nodep/myAmp/sym/inrush.asc

C1: cap; 330n
C2: cap; 1000µ
C3: cap; 330n
C4: cap; 1000µ
M1: nmos; irfs52n15d
M2: pmos; irf4905
R1: res; 470k
R2: res; 470k
R3: res; 1Meg
R4: res; 1Meg
Rload_m: res; 100
Rload_p: res; 100
Rtest_n: res; 1µ
Rtest_r: res; 1µ
V1: voltage; 25
V2: voltage; 25
Named nets: 0, gn, gp, sp
.tran 1 startup
.inc irfs52n15d.txt
.inc irf4905.txt
