nodep/myAmp/sym/mixer.asc

C1: cap; 1µ
C2: cap; 1µ
C3: cap; 10µ
R1: res; 10k
R3: res; 10k
R4: res; 10k
R5: res; 10k
R6: res; {dry*10k + 1m}
R7: res; {(1 - dry)*10k + 1m}
R8: res; 470k
R9: res; {vol*22k + 1m}
U1: opamp2; tl072
V1: voltage; SINE(0 1 1k)
V2: voltage; SINE(0 1 2k3)
V3: voltage; 5
V4: voltage; 2.5
Named nets: 0, VCC, VREF, dry, wet, out
.option numdgt = 7
.option plotwinsize = 0
.inc TL072.sub
.param dry 1
.param vol 1
.tran 0 10m 0 1u
