nodep/myAmp/sym/preamp-esp27.asc

C1: cap; 100n
C2: cap; 22n
C3: cap; 1µ
C4: cap; 120p
C5: cap; 250p
C6: cap; 100n
C7: cap; 47n
C8: cap; 1µ
C10: cap; 120p
C11: cap; 2µ2
D1: diode; 1N4148
D2: diode; 1N4148
D3: diode; 1N4148
D4: diode; 1N4148
P1a: res; {(1 - ptt)*250k + 1m}
P1b: res; {ptt*250k + 1m}
P2: res; {ptb*250k + 1m}
P3: res; {ptm*10k + 1m}
P5a: res; {(1 - ptv)*50k + 1m}
P5b: res; {ptv*50k + 1m}
R1: res; 100k
R3: res; 1Meg
R4: res; 1k
R5: res; 1k
R6: res; 10k
R7: res; 10k
R8: res; 100k
R9: res; 1k
R10: res; 1Meg
R11: res; 10k
R12: res; 10k
R13: res; 4k7
R14: res; 220
R15: res; 2k2
R16: res; 100k
R17: res; 220
R18: res; 10k
R19: res; 1Meg
U1: opamp2; TL072
U2: opamp2; TL072
U3: opamp2; TL072
U4: opamp2; TL072
V1: voltage; SINE(0 0.8 3k); AC 1
V2: voltage; 24
V3: voltage; 12
Named nets: VGND, 0, Vpow, out, in, stage1, stage2, stage3, clipped
.inc OPAx134.lib
.inc NE5532.txt
.inc TL072.sub
.tran 20m
.param ptt 1
.param ptm 1
.param ptb 1
.param ptv 1
