nodep/myAmp/src/app.cpp

#include <stdio.h>
#include <stdlib.h>

#include <avr/io.h>
#include <avr/pgmspace.h>
#include <util/delay.h>

#include "hw.h"
#include "avrdbg.h"
#include "app.h"
#include "adc.h"
#include "powamp.h"
#include "programs.h"
#include "graphtext.h"

App::App()
{
	display.init();
	fill(display, colBlack);
	display.backlight_on();

	//ts.init();

	// init the ADC sources
	adc.set_muxpos(0, ADC_MUXPOS_AIN7_gc, 0);
	adc.set_muxpos(1, ADC_MUXPOS_AIN10_gc, 32);
	adc.set_muxpos(2, ADC_MUXPOS_AIN11_gc, 32);
	adc.set_muxpos(3, ADC_MUXPOS_AIN12_gc, 32);
	adc.set_muxpos(4, ADC_MUXPOS_AIN13_gc, 32);

	Preset::dump_eeprom_presets();

	////testing fonts
	//hline(display, 0, 0, 320, colRed);
	//set_large_font(FreeSans9pt7b);			print_large(display, "P",  5, 0, colYellow);
	//set_large_font(FreeSans12pt7b);			print_large(display, "P", 20, 0, colYellow);
	//set_large_font(FreeSans18pt7b);			print_large(display, "P", 37, 0, colYellow);
	//set_large_font(FreeSans24pt7b);			print_large(display, "P", 55, 0, colYellow);
	//set_large_font(FreeSansBold9pt7b);		print_large(display, "P", 80, 0, colYellow);
	//set_large_font(FreeSansBold12pt7b);		print_large(display, "P", 95, 0, colYellow);
	//set_large_font(FreeSansBold18pt7b);		print_large(display, "P", 115, 0, colYellow);
	//set_large_font(FreeSansBold24pt7b);		print_large(display, "P", 135, 0, colYellow);
	//while (1);

	// wait until the ADC stabilizes
	for (int8_t i = 0; i < 10; i++)
	{
		while (!adc.has_fresh_set())
			;
	}

	// draw the pedals
	draw_exp_pedal(90, 185, colWhite);
	draw_ftsw_pedal(190, 180, colWhite);

	// load the active preset
	Preset preset;
	preset.load_active_prog();
	fv1.set_preset(preset);
	refresh_preset();

	pedals.reset();
}

void App::poll()
{
	powamp_poll();

	Preset current_preset = fv1.get_active_preset();

	// check and handle the ADC
	if (adc.has_fresh_set())
	{
		// convert ADC result to voltage
		refresh_voltage(adc.results[0] / ADC_VOLTAGE_FACTOR);

		if (adc.has_changed[1])
			current_preset.pots[0] = 0x1000 - (adc.results[1] >> 4);

		if (adc.has_changed[2])
			current_preset.pots[1] = 0x1000 - (adc.results[2] >> 4);

		if (adc.has_changed[3])
			current_preset.pots[2] = 0x1000 - (adc.results[3] >> 4);

		if (adc.has_changed[4]  &&  !exp_pedal_active)
			current_preset.mix = 0xff - (adc.results[4] >> 8);
	}

	bool preset_saved = false;
	const auto button_event = rotenc.get_button_event();
	if (button_event == RotEnc::beDouble)
		preset_saved = current_preset.save();
	else if (button_event != RotEnc::beNone)
		dprint("button event: %s\n", RotEnc::get_button_event_desc(button_event));

	const auto delta = rotenc.get_delta();
	if (delta)
	{
		int16_t new_prog_num = current_preset.prog_num + delta;
		if (new_prog_num < 0)
			new_prog_num = NUM_FV1_PROGRAMS - 1;
		if (new_prog_num >= NUM_FV1_PROGRAMS)
			new_prog_num = 0;

		// load the preset if it changed
		if (current_preset.prog_num != new_prog_num)
		{
			current_preset.load(new_prog_num);
			current_preset.save_active_prog();
		}
	}

	// handle pedal events
	for (;;)
	{
		const PedalEvent event = pedals.get_event();

		if (event == evNone)
			break;
			
		if (event == evExpPosition)
		{
			dprint("evExpPos\n");

			if (exp_pedal_active)
			{
				const uint16_t exp_range = pedals.get_position_range();
				if (exp_range)
				{
					const double dest_range = 0x100;
					const double factor = exp_range / dest_range;
					const uint16_t calib_pos = static_cast<uint16_t>(pedals.exp_position / factor);
					current_preset.mix = calib_pos > 0xff ? 0xff : calib_pos;
				}
			}
		}
		else if (event == evExpInit)
		{
			dprint("evExpInit\n");

			pedals.set_led(ledExpGreen);
			pedals.clear_led(ledExpRed);

			// exp pedal is present but not active
			exp_pedal_active = false;
		}
		else if (event == evExpBtnDown)
		{
			dprint("evExpBtnDown\n");

			exp_pedal_active = !exp_pedal_active;
			if (exp_pedal_active)
				pedals.set_led(ledExpRed);
			else
				pedals.clear_led(ledExpRed);
		}
		else if (event == evFtswInit)
		{
			dprint("evFtswInit\n");
			pedals.set_ftsw_number(current_preset.prog_num);
		}
		else if (event == evFtswBtn1Down)
		{
			uint8_t new_prog_num = current_preset.prog_num + 1;
			if (new_prog_num >= NUM_FV1_PROGRAMS)
				new_prog_num = 0;

			current_preset.load(new_prog_num);
			current_preset.save_active_prog();

			pedals.set_led(ledFtswModeTuner);
		}
		else if (event == evFtswBtn1Up)
		{
			pedals.clear_led(ledFtswModeTuner);
		}
		else if (event == evFtswBtn2Down)
		{
			pedals.set_led(ledFtswQA1);
		}
		else if (event == evFtswBtn2Up)
		{
			pedals.clear_led(ledFtswQA1);
		}
		else if (event == evFtswBtn3Down)
		{
			pedals.set_led(ledFtswQA2);
		}
		else if (event == evFtswBtn3Up)
		{
			pedals.clear_led(ledFtswQA2);
		}
		else if (event == evFtswBtn4Down)
		{
			pedals.set_led(ledFtswQA3);
		}
		else if (event == evFtswBtn4Up)
		{
			pedals.clear_led(ledFtswQA3);
		}
	}

	if (fv1.set_preset(current_preset)  ||  preset_saved)
	{
		//dprint("prog=%u P0=%u P1=%u P2=%u mix=%u\n",
		//		current_preset.prog_num,
		//		current_preset.pots[0],
		//		current_preset.pots[1],
		//		current_preset.pots[2],
		//		current_preset.mix);

		refresh_preset();

		// change the number on the footswitch
		if (pedals.ftsw_present)
			pedals.set_ftsw_number(current_preset.prog_num);
	}
}

void App::refresh_voltage(const double battery_voltage)
{
	static uint16_t prev_refresh = 0;
	if (Watch::has_ms_passed_since(2000, prev_refresh))
	{
		// calc the length of the voltage bar
		static uint16_t prev_charge = 0;
		uint16_t curr_charge = 0;
		if (battery_voltage > MIN_VOLTAGE)
		{
			constexpr double factor = Display::Height / (MAX_VOLTAGE - MIN_VOLTAGE);
			curr_charge = static_cast<uint16_t>((battery_voltage - MIN_VOLTAGE) * factor);
			if (curr_charge > Display::Height)
				curr_charge = Display::Height;
		}

		// draw the bar if it changed
		Coord y = 0;
		Coord height = 0;
		if (curr_charge < prev_charge)
			y = Display::Height - prev_charge, height = prev_charge - curr_charge;
		else if (curr_charge > prev_charge)
			y = Display::Height - curr_charge, height = curr_charge - prev_charge;

		if (height != 0)
			fill_rect(display, 0, y, VOLTAGE_BAR_WIDTH, height, colGreen);

		// print the voltage
		static char prev_buff[6] = {0};
		char buff[6];
		sprintf(buff, "%.1fV", battery_voltage);
		if (strcmp(buff, prev_buff) != 0)
		{
			Window<48, 16> win(colBlack);
			set_large_font(FreeSans9pt7b);
			print_large(win, buff, 0, 0, colGreen);
			display.blit(win, VOLTAGE_BAR_WIDTH + 2, Display::Height - win.Height);
			strcpy(prev_buff, buff);
		}

		prev_charge = curr_charge;
		prev_refresh = Watch::now();
	}
}

void App::refresh_preset()
{
	//const auto start = Watch::now();
	static uint8_t prev_prog = 0xff;

	const Preset& preset = fv1.get_active_preset();

	// names
	char name[LONGEST_NAME];
	if (prev_prog != preset.prog_num)
	{
		// center the program name
		{
			Window<WIN_WIDTH, NAME_HEIGHT> win(colBlack);
			set_large_font(FreeSans12pt7b);
			fv1_programs[preset.prog_num].copy_name(name);

			const Coord width = get_text_width_large(name);
			const Coord x_offset = width < win.Width ? (win.Width - width) / 2 : 0;
			print_large(win, name, x_offset, 0, colWhite);
			display.blit(win, VOLTAGE_BAR_WIDTH + WIN_OFFSET, 10);
		}
			
		// print the program number
		{
			char num[4];
			sprintf(num, "%u", preset.prog_num);
			Window<44, 20> win(colBlack);
			set_large_font(FreeSans12pt7b);
			print_large(win, num, 0, 0, colWhite);
			display.blit(win, VOLTAGE_BAR_WIDTH + WIN_OFFSET, 180);
		}

		// param names
		Window<HBAR_WIDTH, PARAM_NAME_HEIGHT> win(colBlack);
		set_large_font(FreeSans9pt7b);
		Coord y_offset = HBAR_YOFFSET + 3;
		for (uint8_t pot = 0; pot < 3; pot++)
		{
			fill(win, colBlack);
			fv1_programs[preset.prog_num].copy_param_name(name, pot);
			if (*name)
				print_large(win, name, 0, 0, colWhite);
			display.blit(win, VOLTAGE_BAR_WIDTH + WIN_OFFSET, y_offset);

			y_offset += HBAR_ADVANCE;
		}

		// we only need to print this once
		static bool dry_wet_printed = false;
		if (!dry_wet_printed)
		{
			fill(win, colBlack);
			print_large(win, "dry/wet", 0, 0, colWhite);
			display.blit(win, VOLTAGE_BAR_WIDTH + WIN_OFFSET, y_offset + MIX_YOFFSET);

			dry_wet_printed = true;
		}

		prev_prog = preset.prog_num;
	}

	// load the saved preset to compare it with the current
	Preset saved_preset;
	saved_preset.load(preset.prog_num);

	for (uint8_t pot = 0; pot < 3; pot++)
	{
		if (fv1_programs[preset.prog_num].is_param_used(pot))
			pot_progbars[pot].draw(display, preset.pots[pot], saved_preset.pots[pot] == preset.pots[pot] ? colWhite : colRed);
		else
			pot_progbars[pot].draw(display, 0, colBlack);
	}

	mix_progbar.draw(display, preset.mix, saved_preset.mix == preset.mix ? colWhite : colRed);

	//const auto diff = Watch::now() - start;
	//if (diff)
	//	dprint("%i %i\n", diff, Watch::ticks2ms(diff));
}

void App::draw_ftsw_pedal(const Coord x, const Coord y, const Color color)
{
	// The Footswitch icon

	// frame
	vline(display, x +   0, y +  2,  38, color);
	hline(display, x +   2, y +  0, 118, color);
	vline(display, x + 120, y +  2,  38, color);
	hline(display, x +   2, y + 40, 118, color);

	// buttons & leds
	auto draw_button = [&](const Coord xb, const Coord yb) {
			draw_pixel(display, xb + 2, yb - 4, color);

			vline(display, xb + 0, yb + 1, 4, color);
			hline(display, xb + 1, yb + 0, 4, color);
			vline(display, xb + 5, yb + 1, 4, color);
			hline(display, xb + 1, yb + 5, 4, color);
		};

	draw_button(x + 18, y + 18);
	draw_button(x + 42, y + 18);
	draw_button(x + 72, y + 18);
	draw_button(x + 96, y + 18);

	// display
	vline(display, x + 54, y + 14,  8, color);
	hline(display, x + 54, y + 14, 12, color);
	vline(display, x + 66, y + 14,  8, color);
	hline(display, x + 54, y + 21, 12, color);
}

void App::draw_exp_pedal(const Coord x, const Coord y, const Color color)
{
	// The Expression Pedal

	// base
	draw_line(display, x +  0, y + 32, x +  4, y + 18, color);
	draw_line(display, x +  4, y + 18, x + 76, y + 24, color);
	draw_line(display, x + 76, y + 24, x + 80, y + 32, color);
	draw_line(display, x +  0, y + 32, x + 80, y + 32, color);

	// line between pedal and base
	draw_line(display, x + 26, y + 12, x + 26, y + 20, color);
	
	// pedal
	draw_line(display, x + 76, y + 24, x + 12, y +  8, color);
	draw_line(display, x + 12, y +  8, x + 16, y +  0, color);
	draw_line(display, x + 16, y +  0, x + 80, y + 12, color);
	draw_line(display, x + 80, y + 12, x + 76, y + 24, color);

	// feet
	draw_line(display, x +  6, y + 33, x +  6, y + 37, color);
	draw_line(display, x +  6, y + 37, x + 16, y + 37, color);
	draw_line(display, x + 16, y + 37, x + 16, y + 33, color);

	draw_line(display, x + 64, y + 33, x + 64, y + 37, color);
	draw_line(display, x + 64, y + 37, x + 74, y + 37, color);
	draw_line(display, x + 74, y + 37, x + 74, y + 33, color);
}
