nodep/myAmp/src/modulo2/hw_setup.h

#pragma once

// the LED shift registers
#define LED_DATA_PORT	B
#define LED_DATA_BIT	3

#define LED_CLOCK_PORT	B
#define LED_CLOCK_BIT	5

#define LED_RST_PORT	B
#define LED_RST_BIT		1

// output pins for selecting the program on the FV-1
// S0, S1 and S2 must be on the same port!!!
#define S0_PORT			C
#define S0_BIT			3

#define S1_PORT			C
#define S1_BIT			2

#define S2_PORT			C
#define S2_BIT			1

#define T0_PORT			C
#define T0_BIT			0

// FV_CLK clock for the FV-1
#define FV_CLK_PORT		B
#define FV_CLK_BIT		2

// rotary encoder
#define ROT_SW_PORT		D
#define ROT_SW_BIT		7

#define ROT_A_PORT		D
#define ROT_A_BIT		6

#define ROT_B_PORT		D
#define ROT_B_BIT		5

// the power amp supervisor
#define PS_MUTE_PORT	D
#define PS_MUTE_BIT		4

#define PS_RESET_PORT	D
#define PS_RESET_BIT	0
