nodep/myAmp/src/avrdbg.h

#pragma once

#ifdef _DEBUG

#include <stdio.h>

# define dprint(...)		printf(__VA_ARGS__)		// gotta love C99, man
# define dprint_P(...)		printf_P(__VA_ARGS__)
# define dprinti(i)			printi(i)
void dbgInit(void);
void printi(uint32_t i);

#else

# define dprint(...)
# define dprint_P(...)
# define dprinti(i)
# define dbgInit()
#endif
